martin-pr/air_monitor/firmware/led/led.ino

// Arduino sketch entry point. All real work lives in app.cpp — this file
// exists only because arduino-cli requires a .ino matching the folder name.
#include "app.h"

void setup() {
    app::setup();
}

void loop() {
    app::loop();
}
